lipoyang/KanpeScouter/mechanical/scouter/STL/barrel.stl

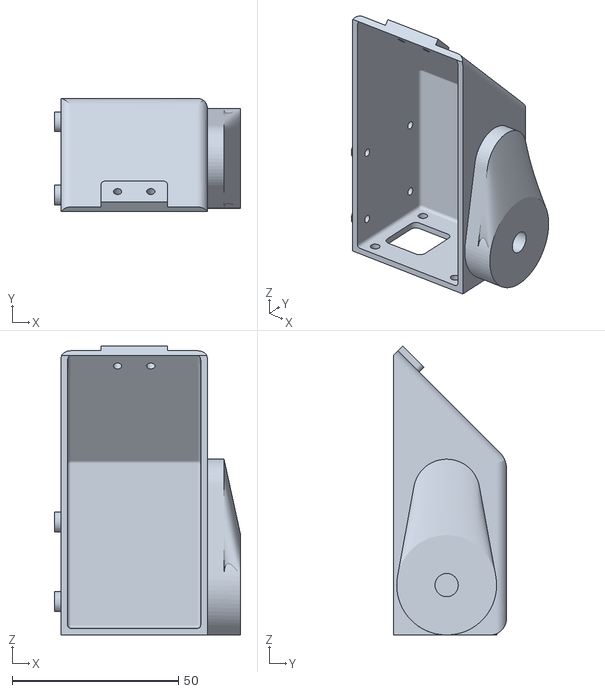
[picture p19: CAD file, 2025-10-11]
mechanical/scouter/STL/barrel.stl
56.0 x 34.0 x 86.8
