lipoyang/KanpeScouter/mechanical/presenter/Presenter_Plate/Component5.step

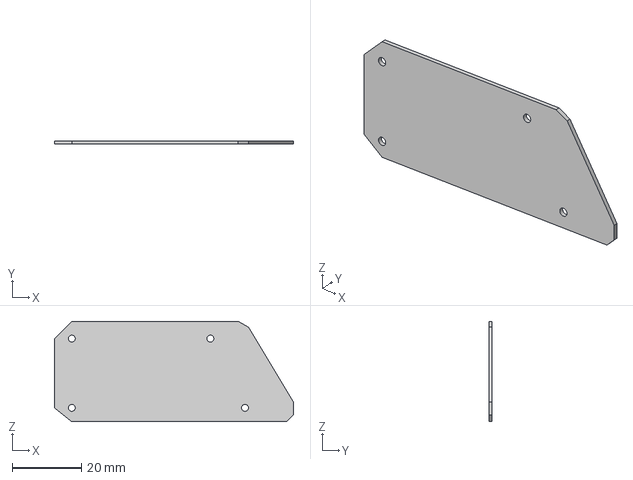
[picture p20: CAD file, 2025-12-28]
mechanical/presenter/Presenter_Plate/Component5.step
69.0 x 1.00 x 29.0 mm
