lipoyang/KanpeScouter/mechanical/presenter/STL/TopBar.stl

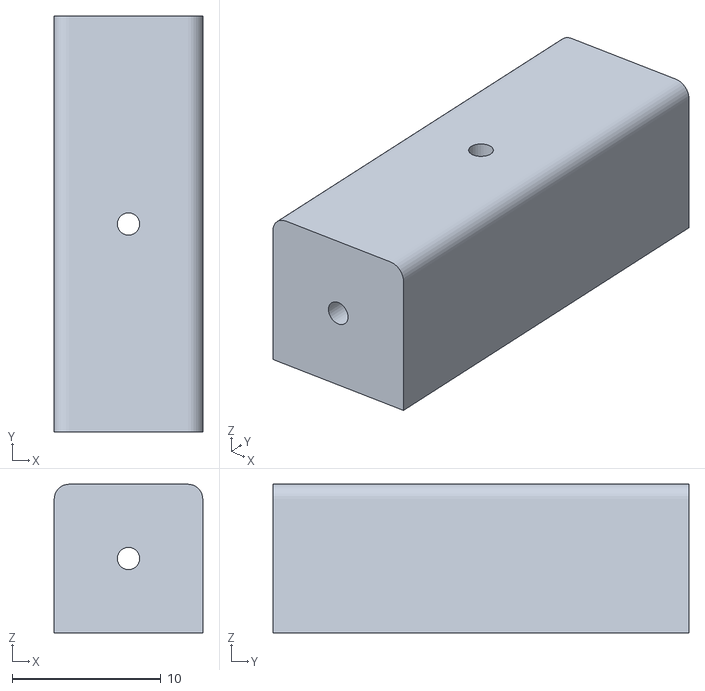
[picture p21: CAD file, 2025-10-11]
mechanical/presenter/STL/TopBar.stl
10.0 x 28.0 x 10.0
