lipoyang/KanpeScouter/mechanical/presenter/Presenter_Plate/Component3.step

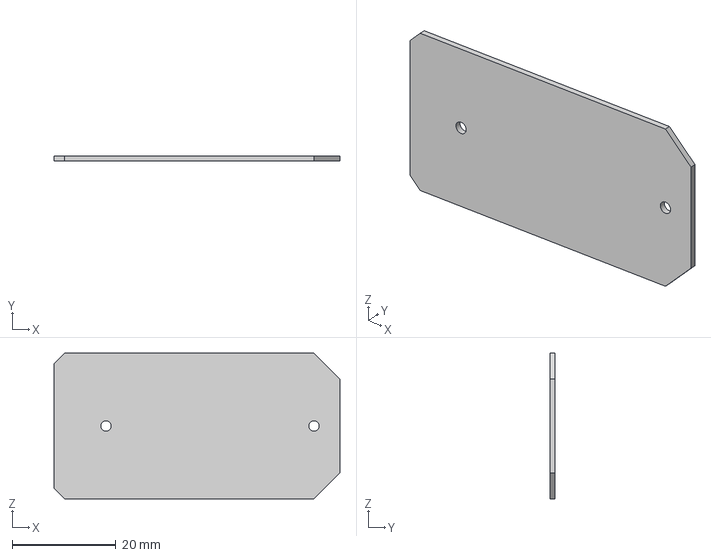
[picture p22: CAD file, 2025-12-28]
mechanical/presenter/Presenter_Plate/Component3.step
55.0 x 1.00 x 28.0 mm
